gumulka/nametag/app/src/nametag.h

#include <zephyr/kernel.h>

int clear_display(const struct device *const display);

int serious_name(const struct device *const display);
int serious_nick(const struct device *const display);
int serious_full_name(const struct device *const display);

int lgbtq_name(const struct device *const display);
int lgbtq_name_extra(const struct device *const display);

int fabilicious_turtli(const struct device *const display);
